awarsewa/aztec/docs/images/aztec_header.png

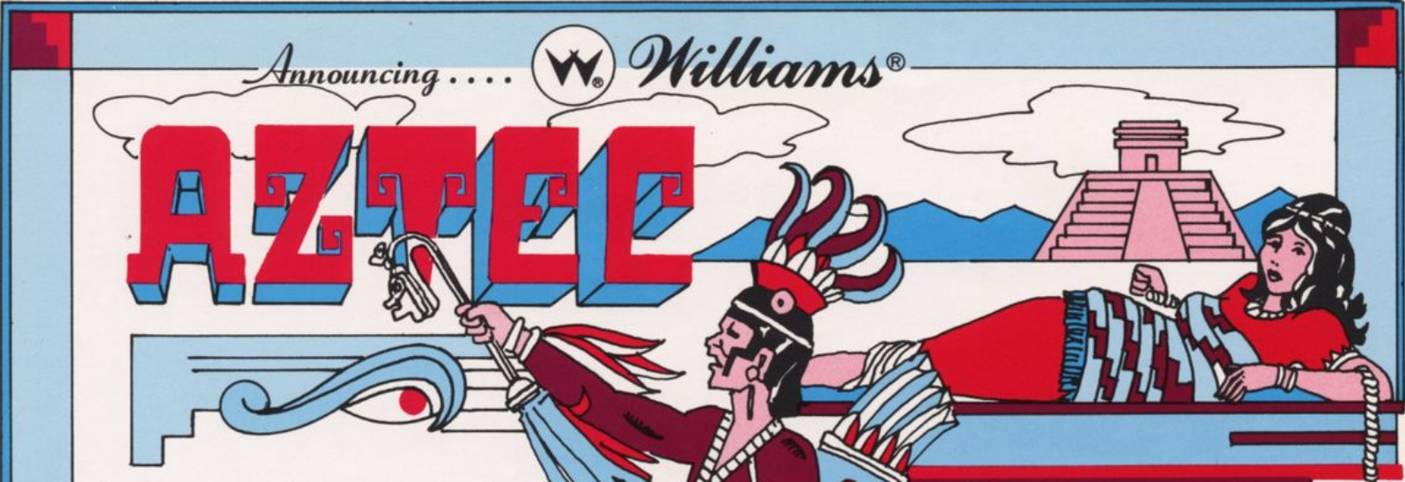
docs/images/aztec_header.png
