awarsewa/aztec/docs/images/aztec_insides.jpg

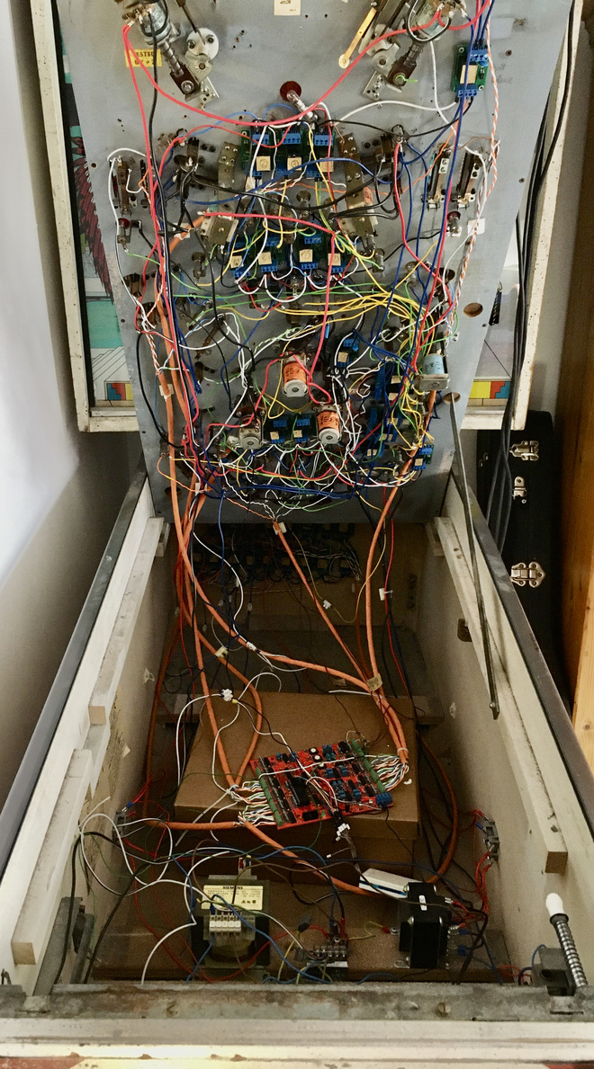
docs/images/aztec_insides.jpg
