awarsewa/aztec/docs/images/IMG_2651.png

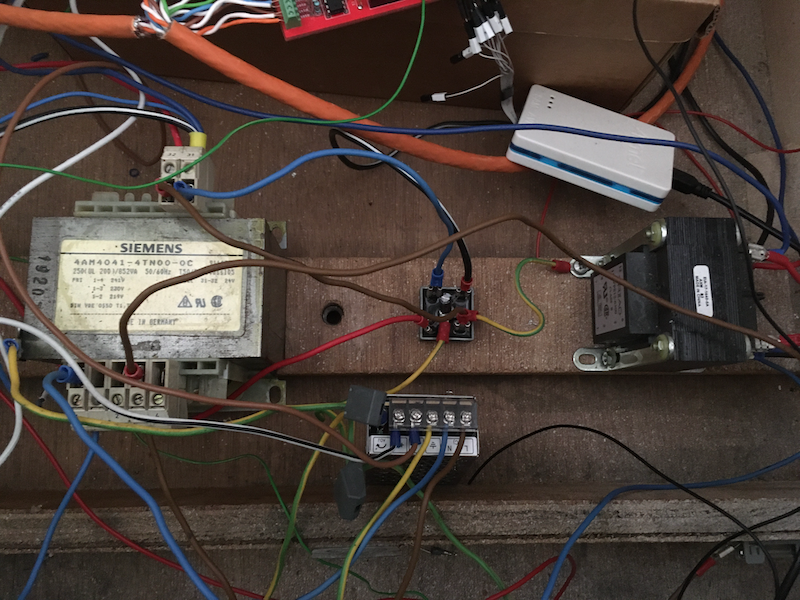
docs/images/IMG_2651.png
