awarsewa/aztec/docs/images/z_relay.png

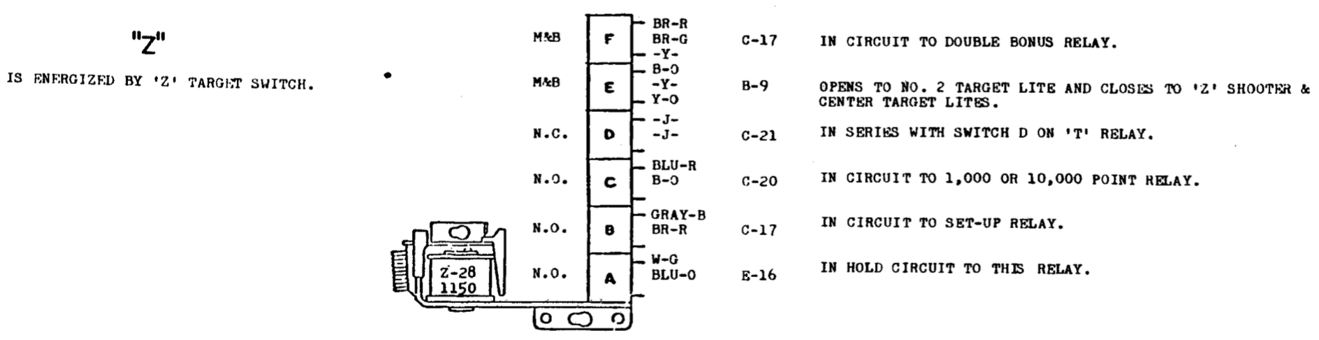
docs/images/z_relay.png
